radiolok/brainfuckpc/doc/core-memory.png

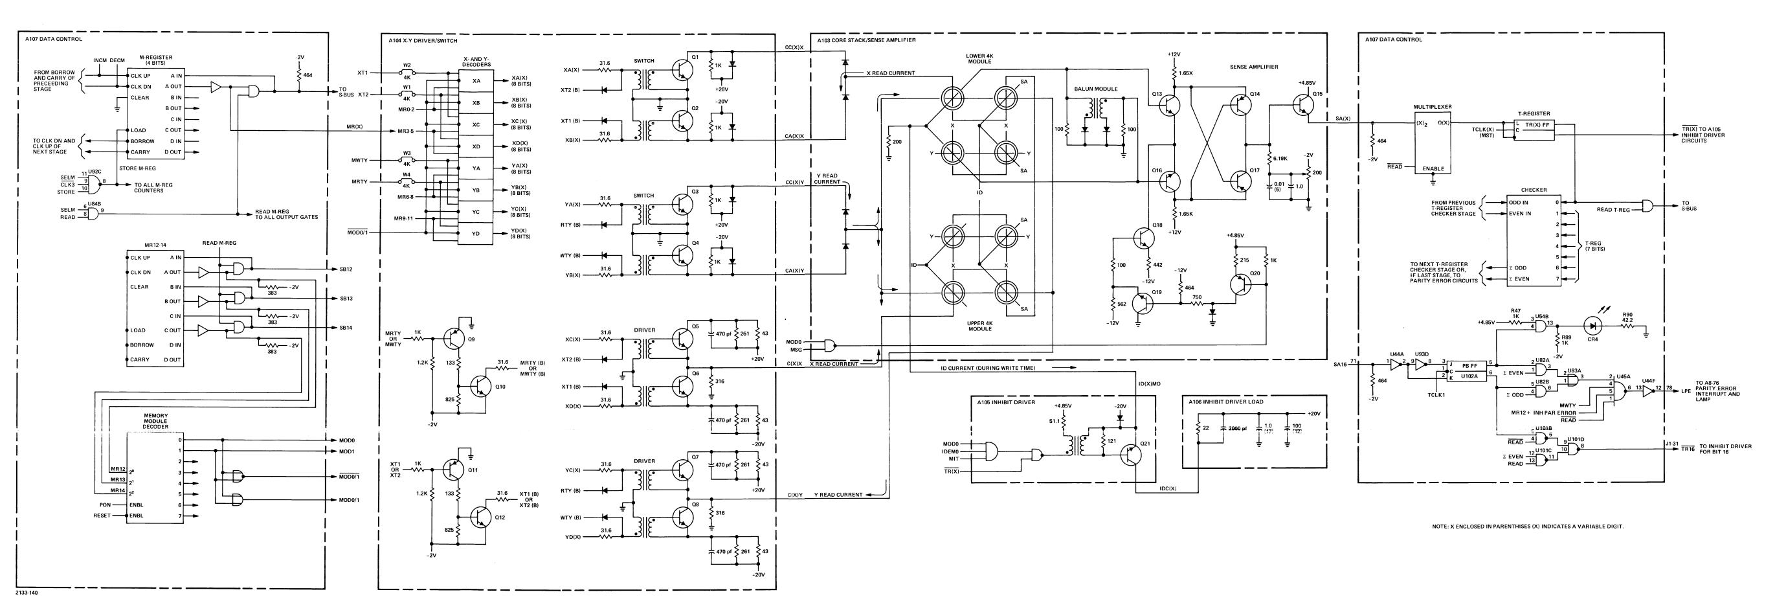
doc/core-memory.png
