radiolok/brainfuckpc/img/1bit_REG.png

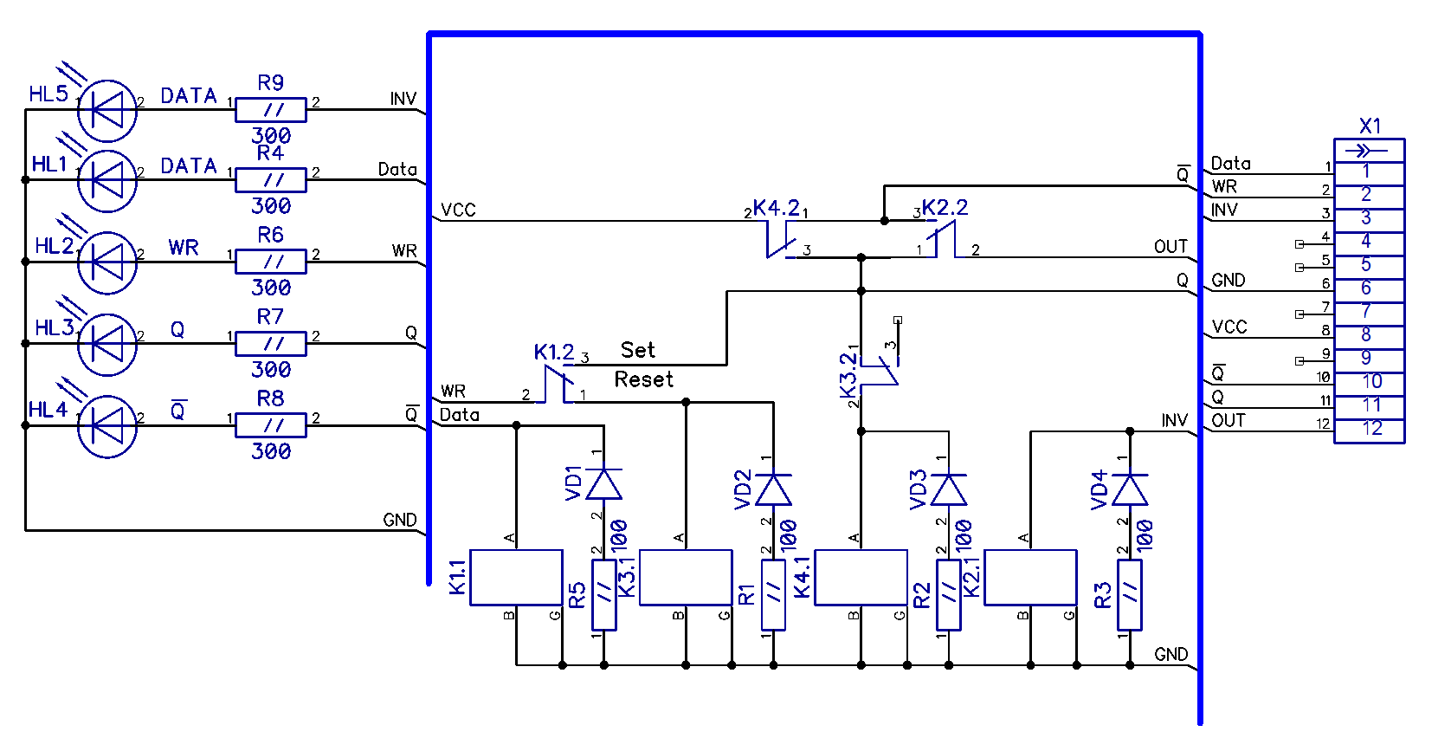
img/1bit_REG.png
