radiolok/brainfuckpc/img/16bit_parallel_SUM.png

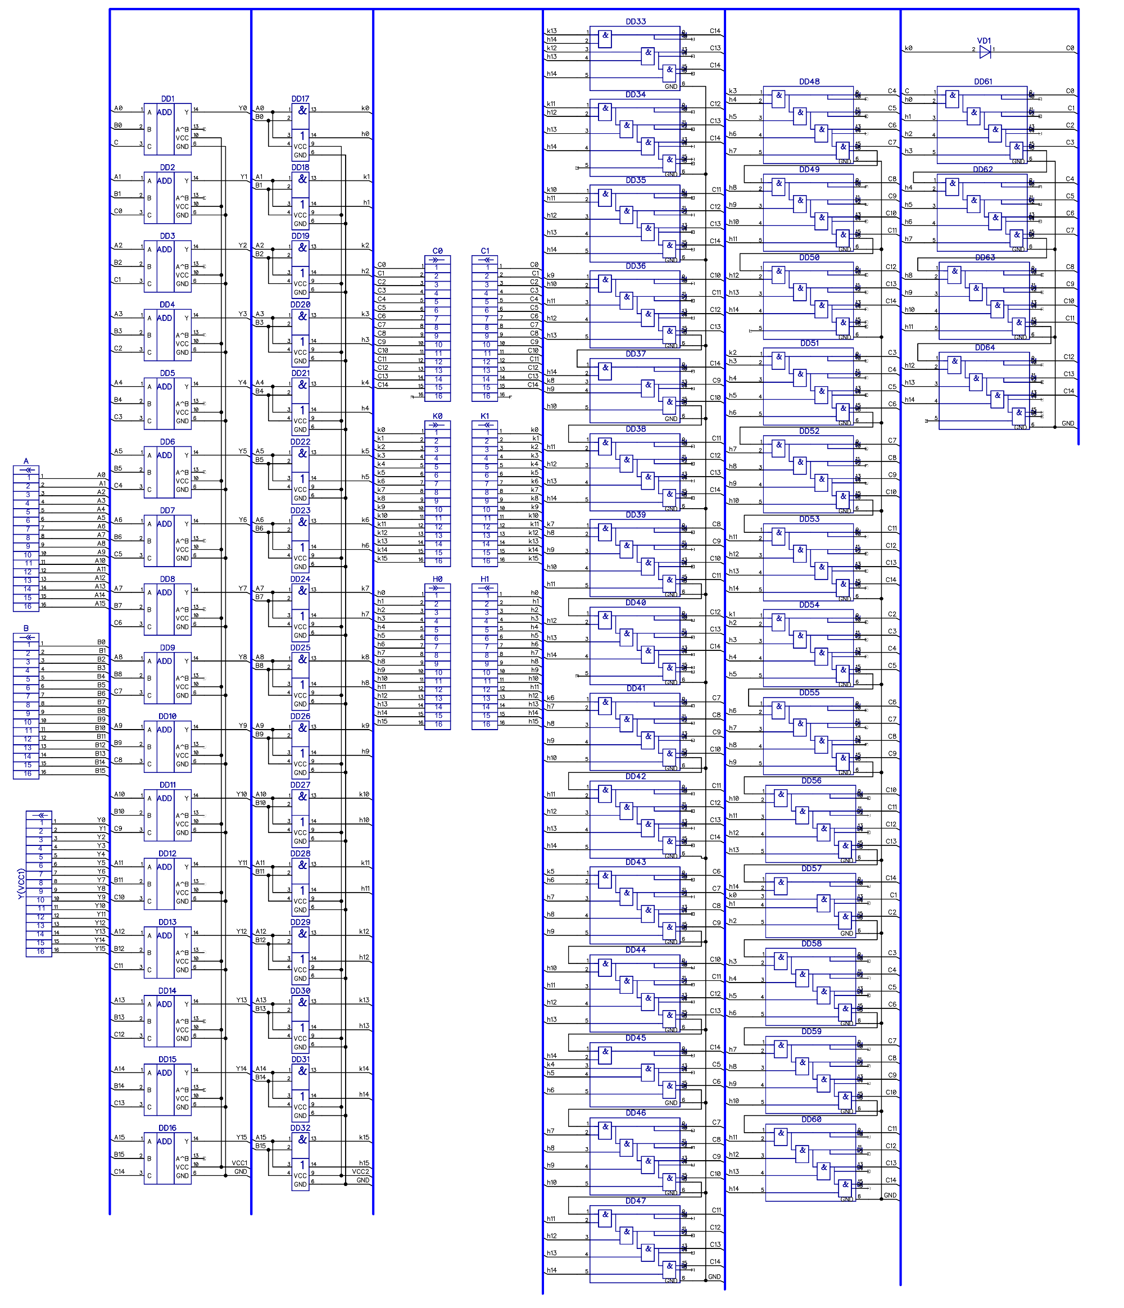
img/16bit_parallel_SUM.png
