radiolok/brainfuckpc/img/ALU.jpg

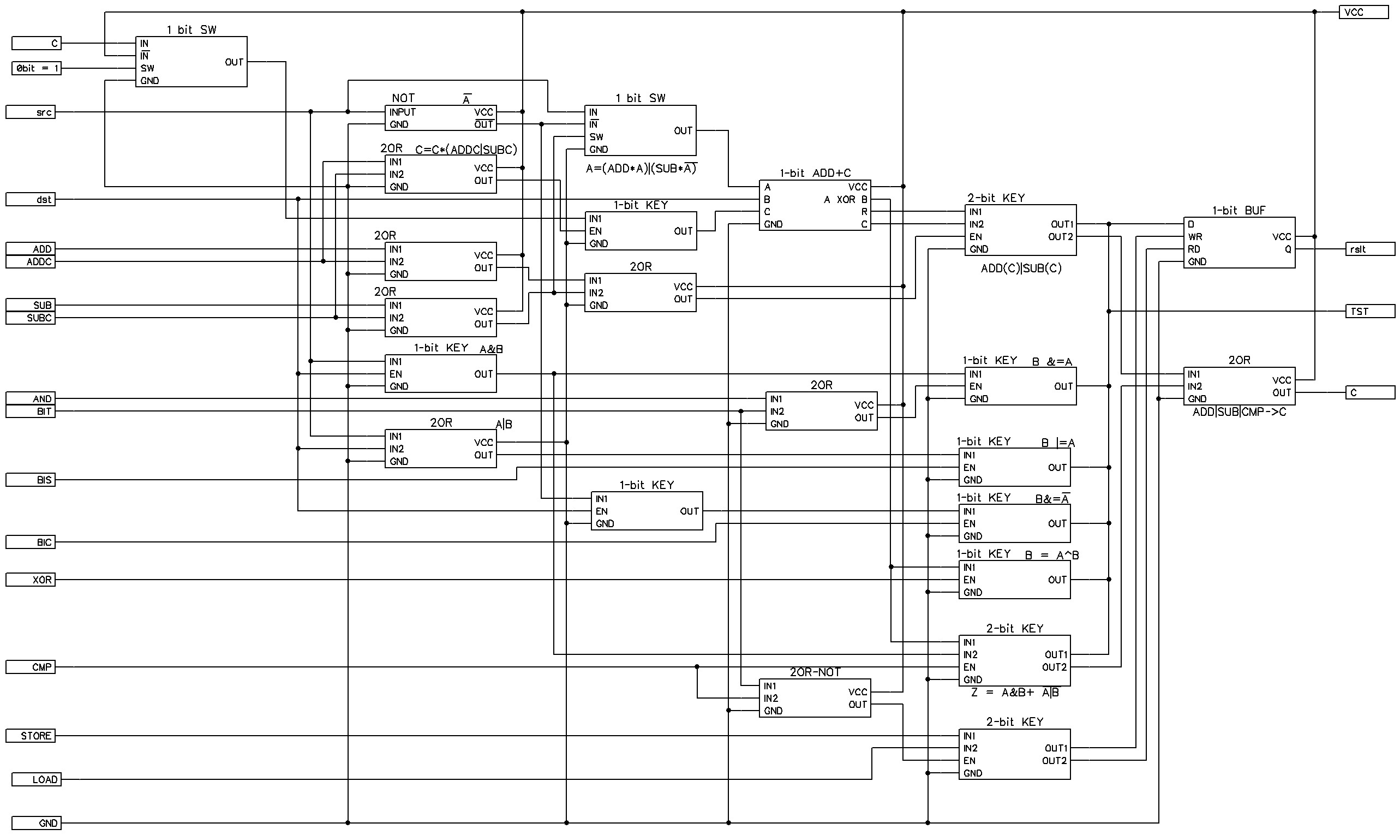
img/ALU.jpg
