radiolok/brainfuckpc/img/base_block_view.jpg

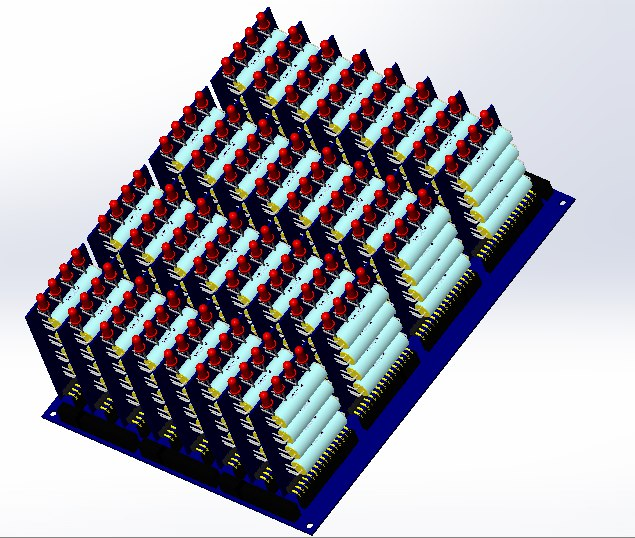
img/base_block_view.jpg
