radiolok/brainfuckpc/img/Brainfuck_PC_main_logic.png

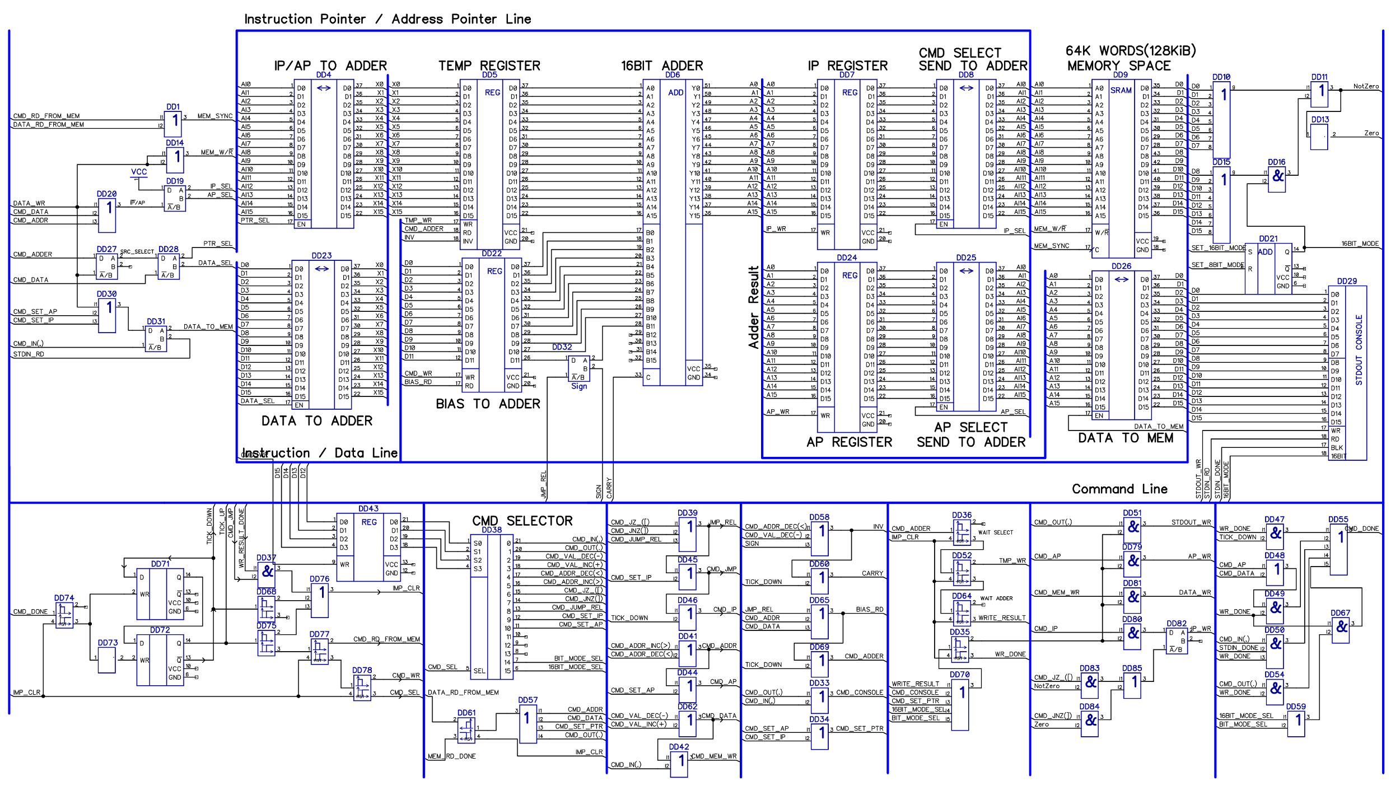
img/Brainfuck_PC_main_logic.png
