radiolok/brainfuckpc/img/ds.jpg

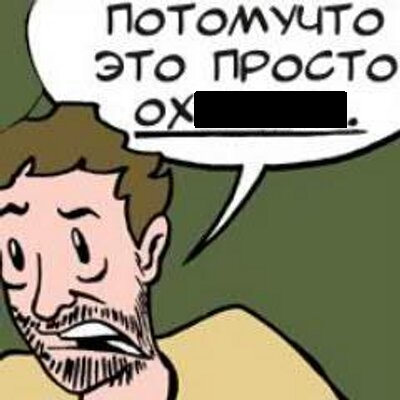
img/ds.jpg
