radiolok/brainfuckpc/img/logic.jpg

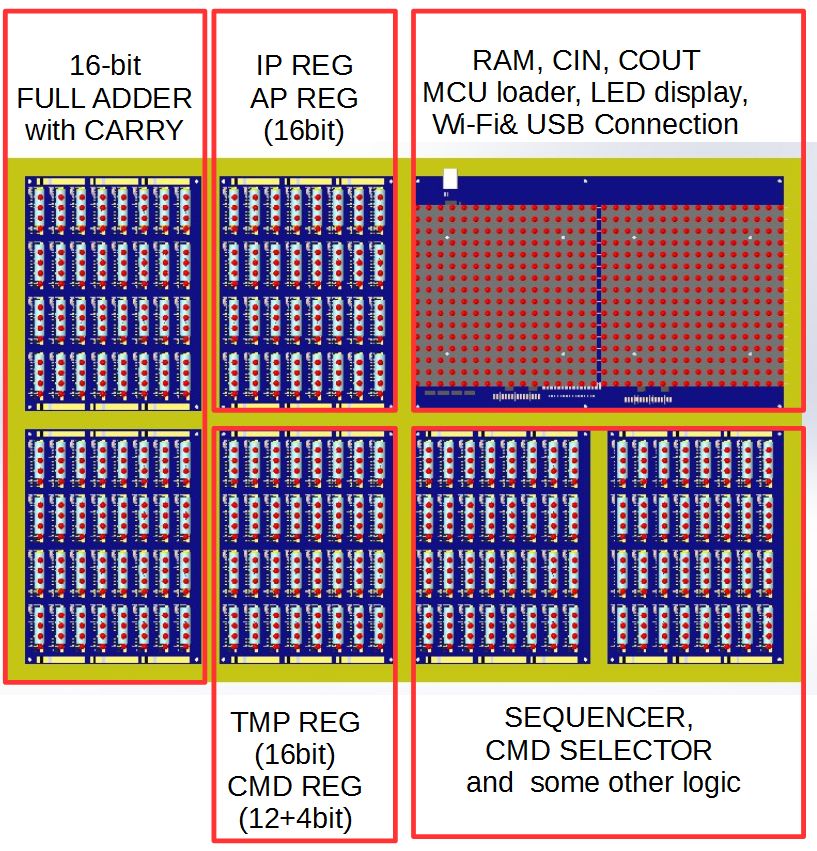
img/logic.jpg
