radiolok/brainfuckpc/img/logic_1.jpg

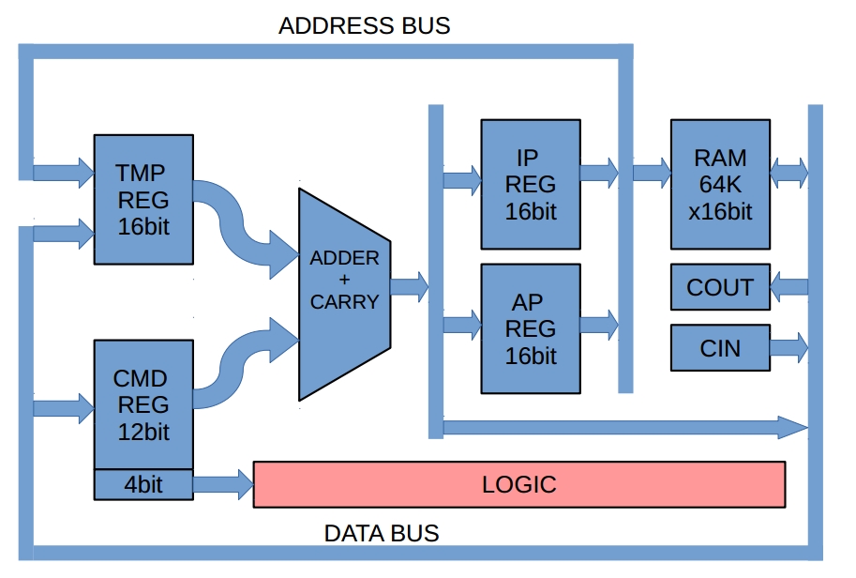
img/logic_1.jpg
