radiolok/brainfuckpc/img/memory_brd_real_2.jpg

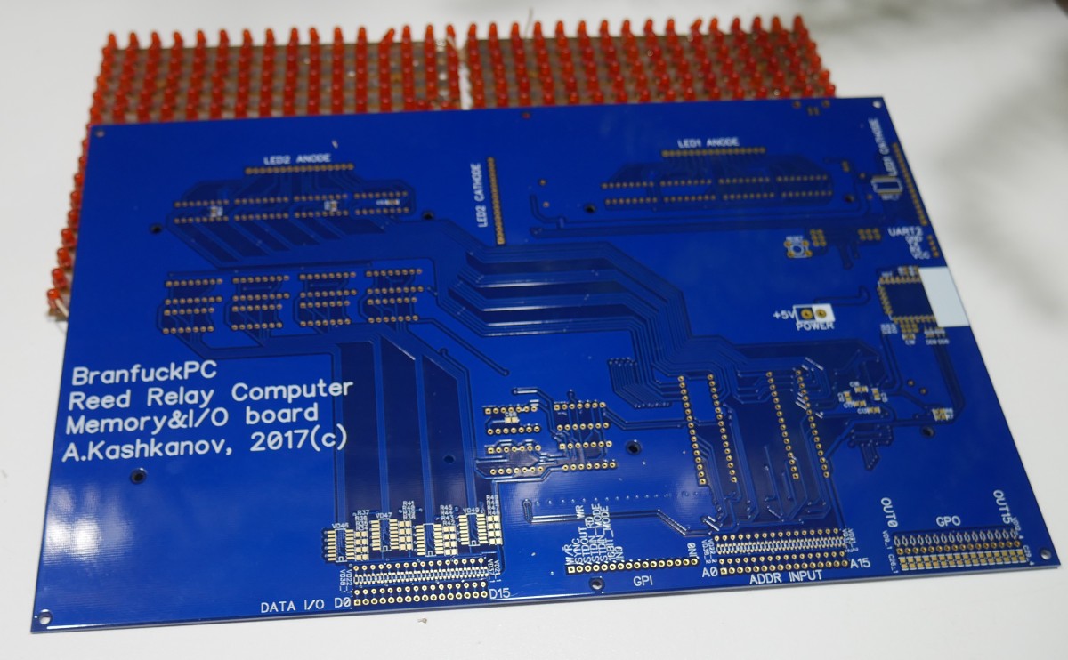
img/memory_brd_real_2.jpg
