radiolok/brainfuckpc/img/memorybrd_3d_bottom.jpg

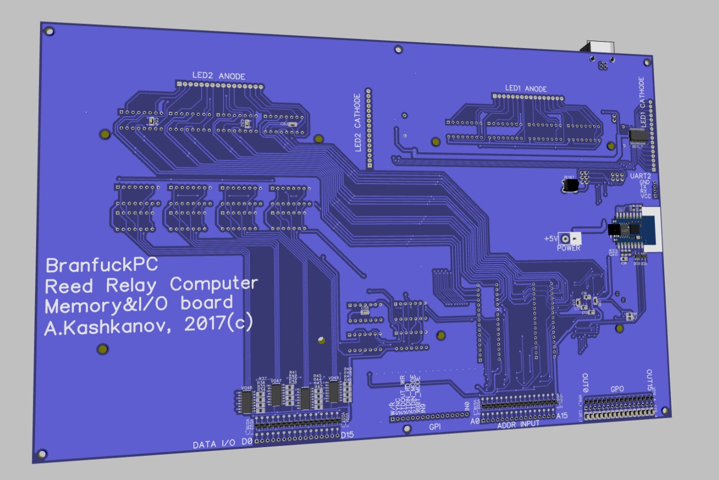
img/memorybrd_3d_bottom.jpg
