radiolok/brainfuckpc/img/module.jpg

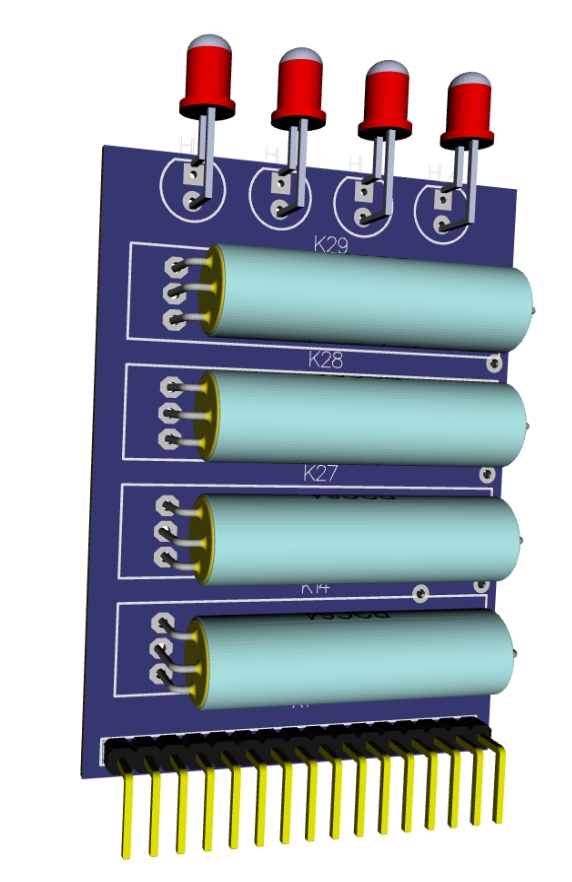
img/module.jpg
