radiolok/brainfuckpc/img/relays.jpg

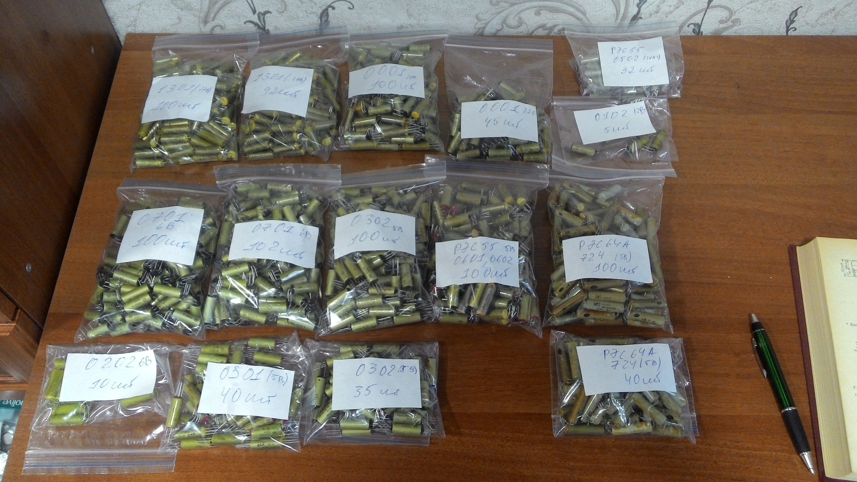
img/relays.jpg
