radiolok/brainfuckpc/img/reley_board.jpg

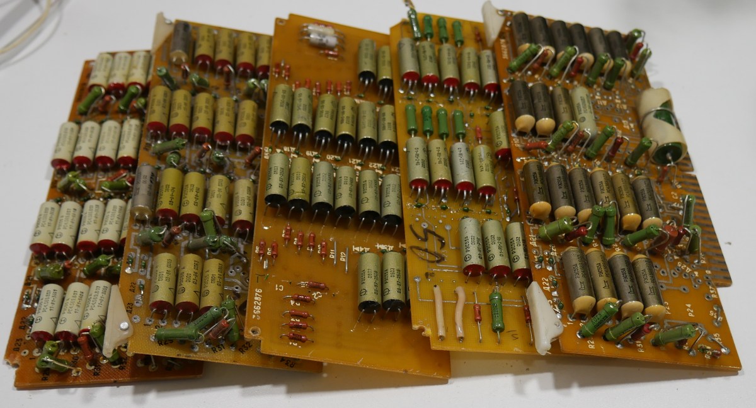
img/reley_board.jpg
