radiolok/brainfuckpc/img/sch1.jpg

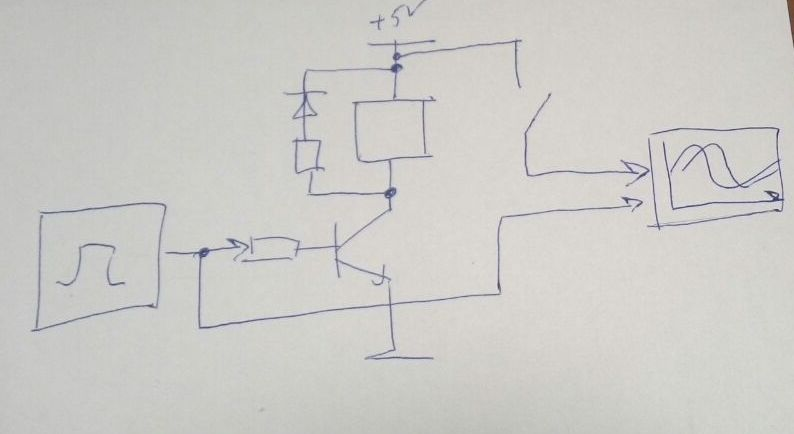
img/sch1.jpg
