radiolok/brainfuckpc/sch/Diode_module/3d_bottom.jpg

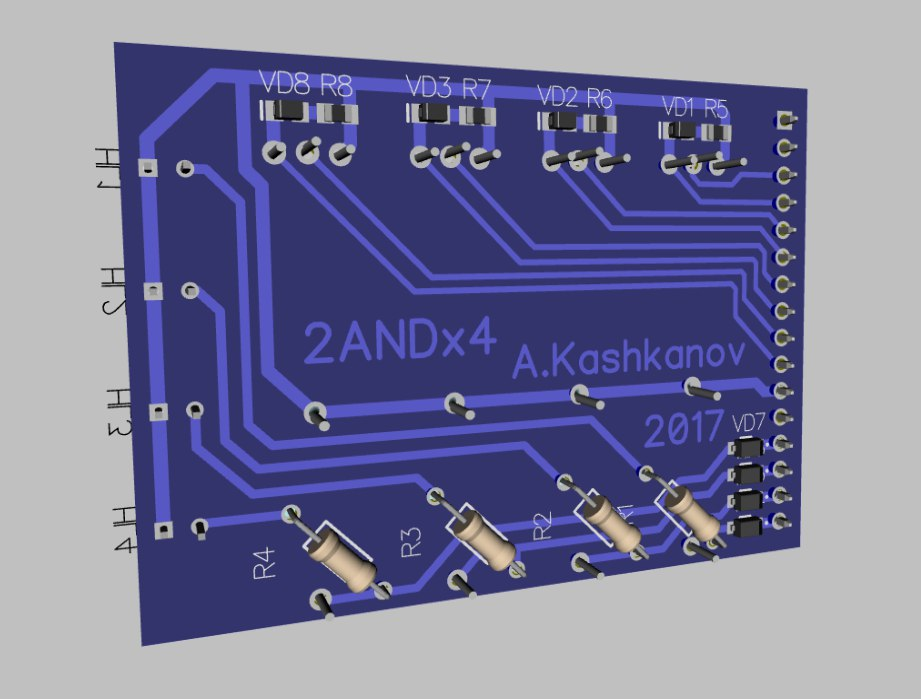
sch/Diode_module/3d_bottom.jpg
