radiolok/brainfuckpc/sch/Diode_module/diode_module.png

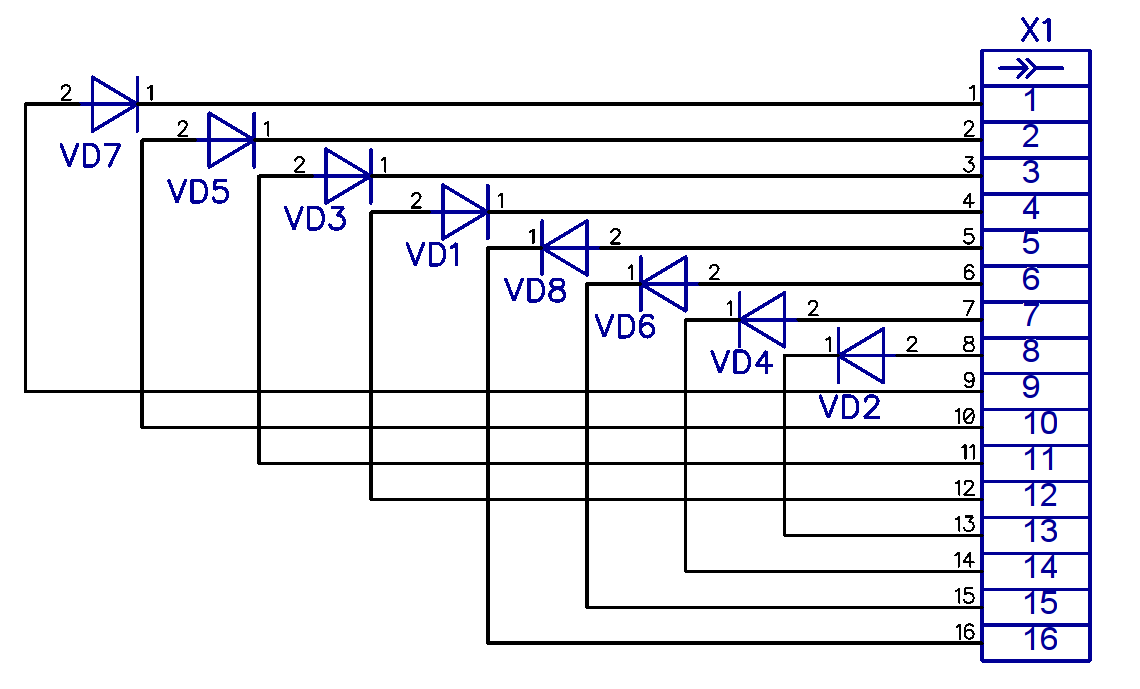
sch/Diode_module/diode_module.png
