radiolok/brainfuckpc/sch/MemoryBrd/pcb_bottom_3d.jpg

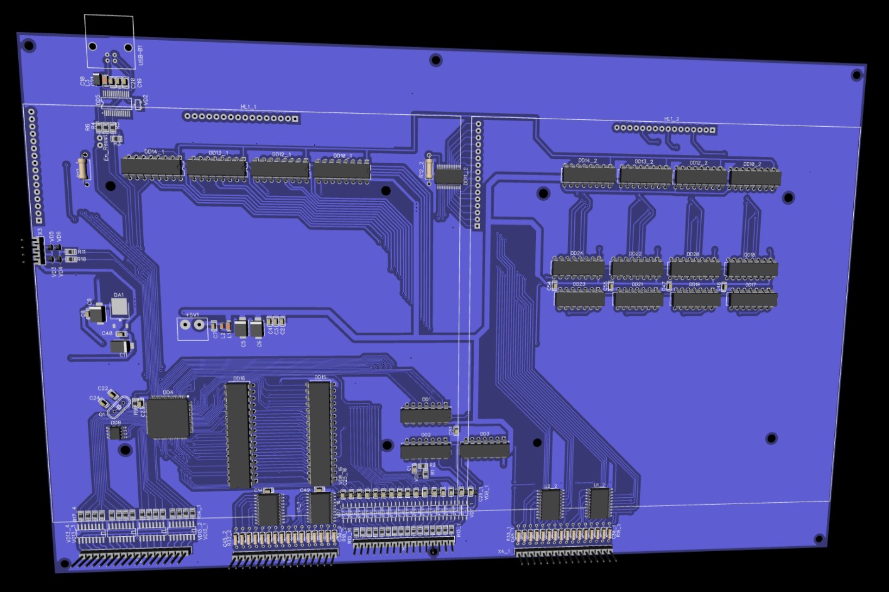
sch/MemoryBrd/pcb_bottom_3d.jpg
