radiolok/brainfuckpc/sch/MemoryBrd/pcb_top_3d.jpg

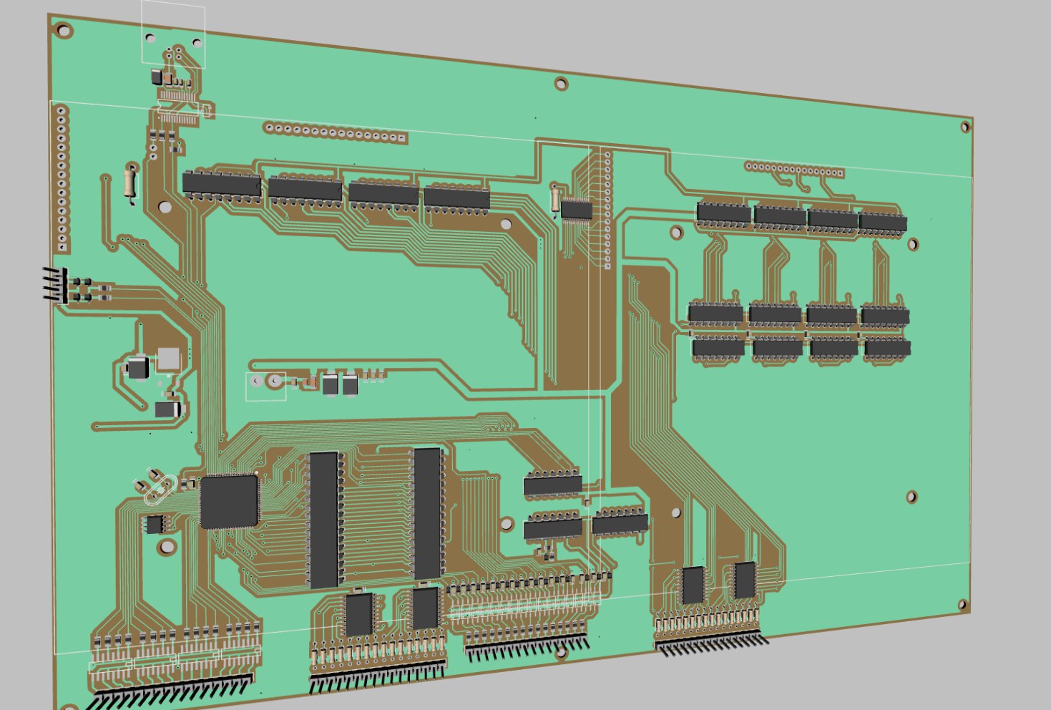
sch/MemoryBrd/pcb_top_3d.jpg
