radiolok/brainfuckpc/waveforms/ada-ads.png

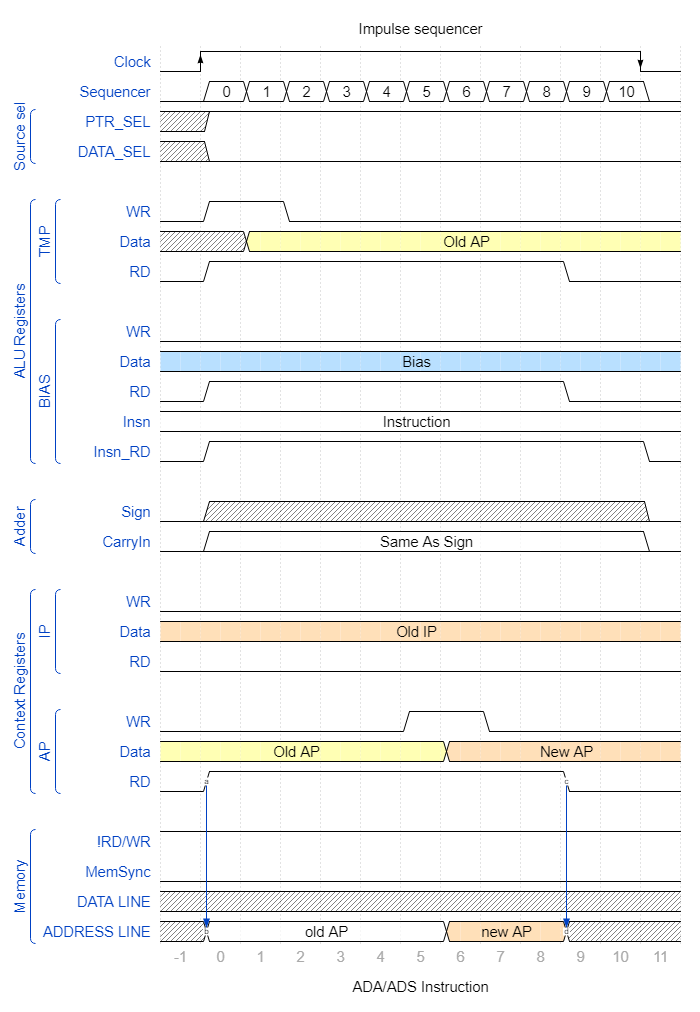
waveforms/ada-ads.png
