radiolok/brainfuckpc/waveforms/add-sub.png

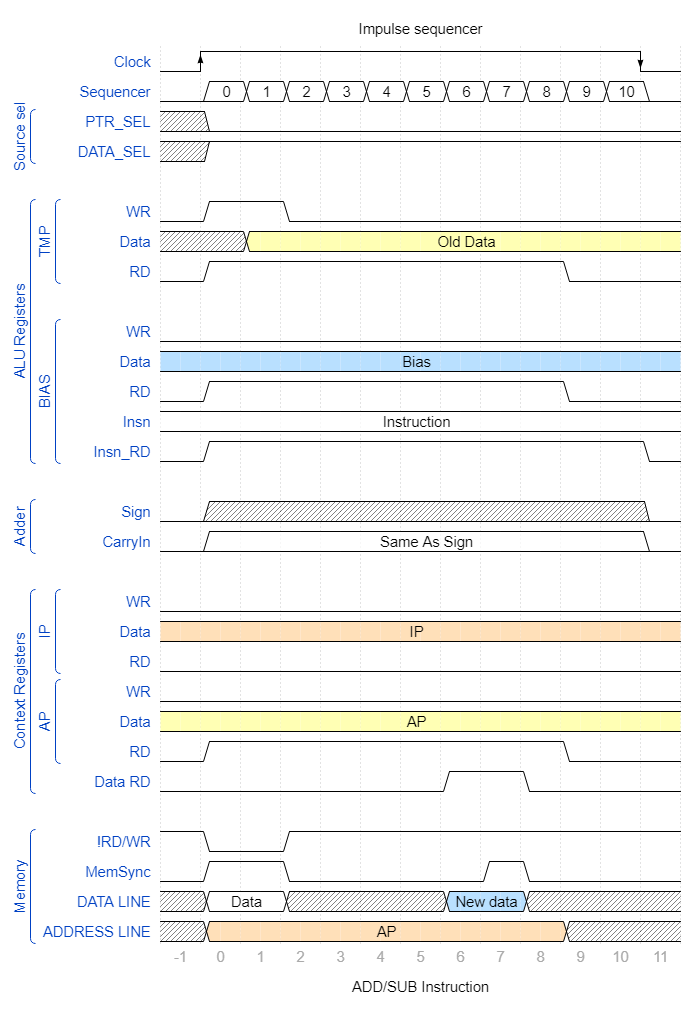
waveforms/add-sub.png
