radiolok/brainfuckpc/waveforms/cout.png

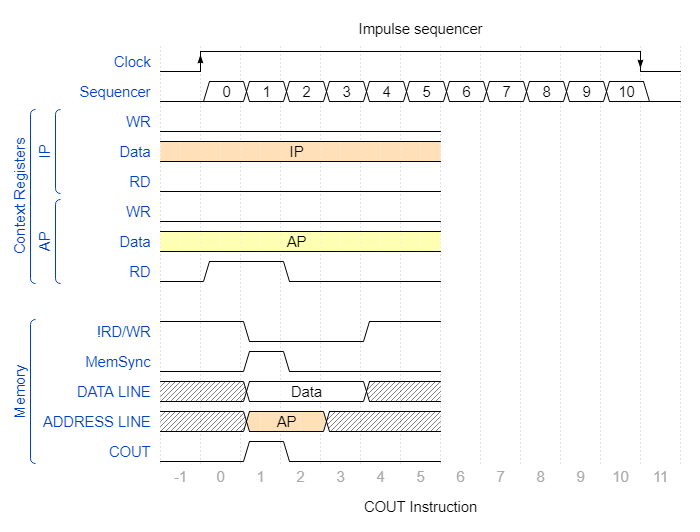
waveforms/cout.png
