radiolok/brainfuckpc/waveforms/insn_fetch.png

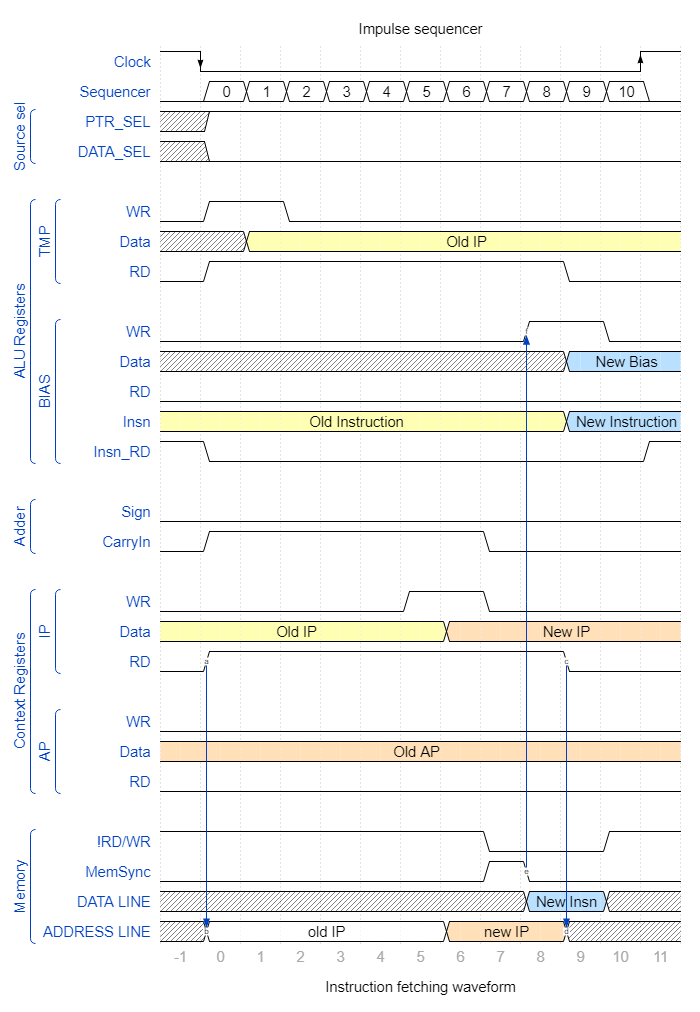
waveforms/insn_fetch.png
