radiolok/brainfuckpc/waveforms/jz_jnz_not_taken.png

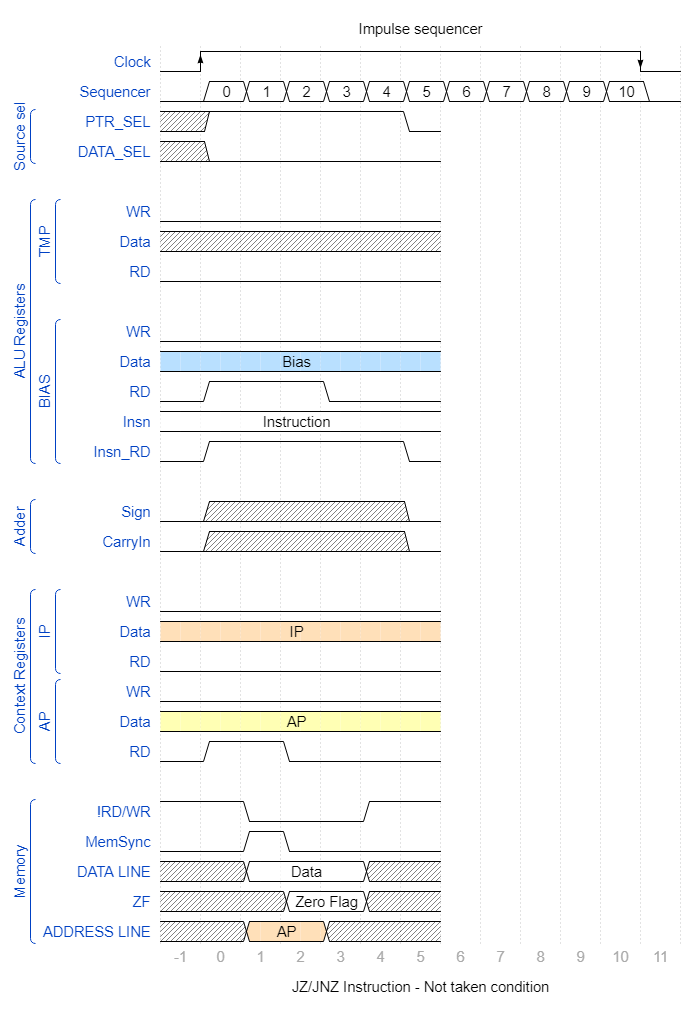
waveforms/jz_jnz_not_taken.png
