radiolok/brainfuckpc/waveforms/jz_jnz_taken.png

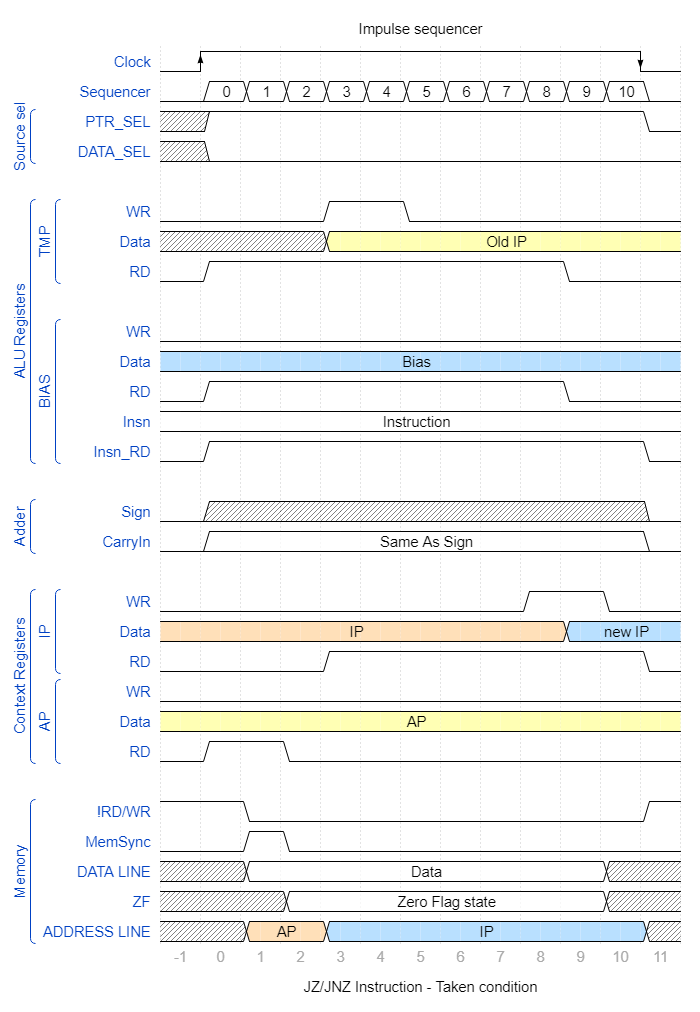
waveforms/jz_jnz_taken.png
