radiolok/brainfuckpc/fw/[DEPRECATE]/memorybrd_freertos/main.c

/*
 * FreeRTOS Kernel V10.1.1
 * Copyright (C) 2018 Amazon.com, Inc. or its affiliates.  All Rights Reserved.
 *
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
 * http://www.FreeRTOS.org
 * http://aws.amazon.com/freertos
 *
 * 1 tab == 4 spaces!
 */

/*
 * Creates all the demo application tasks, then starts the scheduler.  The WEB
 * documentation provides more details of the demo application tasks.
 *
 * Main. c also creates a task called "Check".  This only executes every three
 * seconds but has the highest priority so is guaranteed to get processor time.
 * Its main function is to check that all the other tasks are still operational.
 * Each task that does not flash an LED maintains a unique count that is
 * incremented each time the task successfully completes its function.  Should
 * any error occur within such a task the count is permanently halted.  The
 * check task inspects the count of each task to ensure it has changed since
 * the last time the check task executed.  If all the count variables have
 * changed all the tasks are still executing error free, and the check task
 * toggles an LED.  Should any task contain an error at any time the LED toggle
 * will stop.
 *
 * The LED flash and communications test tasks do not maintain a count.
 */

/*
Changes from V1.2.0

	+ Changed the baud rate for the serial test from 19200 to 57600.

Changes from V1.2.3

	+ The integer and comtest tasks are now used when the cooperative scheduler
	  is being used.  Previously they were only used with the preemptive
	  scheduler.

Changes from V1.2.5

	+ Set the baud rate to 38400.  This has a smaller error percentage with an
	  8MHz clock (according to the manual).

Changes from V2.0.0

	+ Delay periods are now specified using variables and constants of
	  TickType_t rather than unsigned long.

Changes from V2.6.1

	+ The IAR and WinAVR AVR ports are now maintained separately.

Changes from V4.0.5

	+ Modified to demonstrate the use of co-routines.

*/

#include <stdlib.h>
#include <string.h>

#ifdef GCC_MEGA_AVR
	/* EEPROM routines used only with the WinAVR compiler. */
	#include <avr/eeprom.h>
#endif

/* Scheduler include files. */
#include "FreeRTOS.h"
#include "task.h"
#include "croutine.h"

/* Demo file headers. */
#include "PollQ.h"
#include "integer.h"
#include "serial.h"
#include "comtest.h"
#include "crflash.h"
#include "print.h"


/* Priority definitions for most of the tasks in the demo application.  Some
tasks just use the idle priority. */
#define mainLED_TASK_PRIORITY			( tskIDLE_PRIORITY + 1 )
#define mainCOM_TEST_PRIORITY			( tskIDLE_PRIORITY + 2 )
#define mainQUEUE_POLL_PRIORITY			( tskIDLE_PRIORITY + 2 )
#define mainCHECK_TASK_PRIORITY			( tskIDLE_PRIORITY + 3 )

/* Baud rate used by the serial port tasks. */
#define mainCOM_TEST_BAUD_RATE			( ( unsigned long ) 38400 )

/* LED used by the serial port tasks.  This is toggled on each character Tx,
and mainCOM_TEST_LED + 1 is toggles on each character Rx. */
#define mainCOM_TEST_LED				( 4 )

/* LED that is toggled by the check task.  The check task periodically checks
that all the other tasks are operating without error.  If no errors are found
the LED is toggled.  If an error is found at any time the LED is never toggles
again. */
#define mainCHECK_TASK_LED				( 7 )

/* The period between executions of the check task. */
#define mainCHECK_PERIOD				( ( TickType_t ) 3000 / portTICK_PERIOD_MS  )

/* An address in the EEPROM used to count resets.  This is used to check that
the demo application is not unexpectedly resetting. */
#define mainRESET_COUNT_ADDRESS			( ( void * ) 0x50 )


static void prvCheckOtherTasksAreStillRunning( void );

/*-----------------------------------------------------------*/

int main( void )
{

	/* In this port, to use preemptive scheduler define configUSE_PREEMPTION
	as 1 in portmacro.h.  To use the cooperative scheduler define
	configUSE_PREEMPTION as 0. */
	vTaskStartScheduler();

	return 0;
}
/*-----------------------------------------------------------*/

static void vErrorChecks( void *pvParameters )
{
static volatile unsigned long ulDummyVariable = 3UL;

	/* The parameters are not used. */
	( void ) pvParameters;

	/* Cycle for ever, delaying then checking all the other tasks are still
	operating without error. */
	for( ;; )
	{
		vTaskDelay( mainCHECK_PERIOD );

		/* Perform a bit of 32bit maths to ensure the registers used by the
		integer tasks get some exercise. The result here is not important -
		see the demo application documentation for more info. */
		ulDummyVariable *= 3;

		prvCheckOtherTasksAreStillRunning();
	}
}
/*-----------------------------------------------------------*/

static void prvCheckOtherTasksAreStillRunning( void )
{
static portBASE_TYPE xErrorHasOccurred = pdFALSE;


}
/*-----------------------------------------------------------*/

static void prvIncrementResetCount( void )
{
unsigned char ucCount;

	eeprom_read_block( &ucCount, mainRESET_COUNT_ADDRESS, sizeof( ucCount ) );
	ucCount++;
	eeprom_write_byte( mainRESET_COUNT_ADDRESS, ucCount );
}
/*-----------------------------------------------------------*/
