radiolok/brainfuckpc/fw/mcuUtil/uart.h

#ifndef UART_H
#define UART_H
/************************************************************************
Title:    Interrupt UART library with receive/transmit circular buffers
Author:   Peter Fleury <pfleury@gmx.ch>   http://jump.to/fleury
Support:   Artem Kashkanov<pcb@rlntech.org> http://hg.rlntech.org/uart
File:     $Id: uart.h,v 1.8.2.1 2007/07/01 11:14:38 peter Exp $
Software: AVR-GCC 4.1, AVR Libc 1.4
Hardware: any AVR with built-in UART, tested on AT90S8515 & ATmega8 at 4 Mhz
License:  GNU General Public License 
Usage:    see Doxygen manual

LICENSE:
    Copyright (C) 2006 Peter Fleury

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
************************************************************************/

/************************************************************************
uart_available, uart_flush, uart1_available, and uart1_flush functions
were adapted from the Arduino HardwareSerial.h library by Tim Sharpe on 
11 Jan 2009.  The license info for HardwareSerial.h is as follows:

  HardwareSerial.h - Hardware serial library for Wiring
  Copyright (c) 2006 Nicholas Zambetti.  All right reserved.

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
  You should have received a copy of the GNU Lesser General Public
  License along with this library; if not, write to the Free Software
  Foundation, Inc., 51 Franklin St, Fifth Floor, Boston, MA  02110-1301  USA
************************************************************************/

/************************************************************************
Changelog for modifications made by Tim Sharpe, starting with the current
  library version on his Web site as of 05/01/2009. 

Date        Description
=========================================================================
05/12/2009  Added Arduino-style available() and flush() functions for both
			supported UARTs.  Really wanted to keep them out of the library, so
			that it would be as close as possible to Peter Fleury's original
			library, but has scoping issues accessing internal variables from
			another program.  Go C!

************************************************************************/

/** 
 *  This library can be used to transmit and receive data through the built in UART. 
 *
 *  An interrupt is generated when the UART has finished transmitting or
 *  receiving a byte. The interrupt handling routines use circular buffers
 *  for buffering received and transmitted data.
 *
 *  The UART_RX_BUFFER_SIZE and UART_TX_BUFFER_SIZE constants define
 *  the size of the circular buffers in bytes. Note that these constants must be a power of 2.
 *  You may need to adapt this constants to your target and your application by adding 
 *  CDEFS += -DUART_RX_BUFFER_SIZE=nn -DUART_RX_BUFFER_SIZE=nn to your Makefile.
 *
 *  @note Based on Atmel Application Note AVR306
 *  @author Peter Fleury pfleury@gmx.ch  http://jump.to/fleury
 */
 


#if (__GNUC__ * 100 + __GNUC_MINOR__) < 304
#error "This library requires AVR-GCC 3.4 or later, update to newer AVR-GCC compiler !"
#endif

#include <stdint.h>

#define UART_BAUD_SELECT(baudRate,xtalCpu) ((xtalCpu)/((baudRate)*16l)-1)


#define UART_BAUD_SELECT_DOUBLE_SPEED(baudRate,xtalCpu) (((xtalCpu)/((baudRate)*8l)-1)|0x8000)


/** Size of the circular receive buffer, must be power of 2 */
#ifndef UART_RX_BUFFER_SIZE
#define UART_RX_BUFFER_SIZE 16
#endif
/** Size of the circular transmit buffer, must be power of 2 */
#ifndef UART_TX_BUFFER_SIZE
#define UART_TX_BUFFER_SIZE 32
#endif



#define UART_FRAME_ERROR      0x00              /* Framing Error by UART       */
#define UART_OVERRUN_ERROR    0x00              /* Overrun condition by UART   */
#define UART_BUFFER_OVERFLOW  0x00              /* receive ringbuffer overflow */
#define UART_NO_DATA          0x00              /* no receive data available   */


#define UART_PARITY_NONE 0x00
#define UART_PARITY_ODD 0x01
#define UART_PARITY_EVEN 0x02


 void uart_init(unsigned int baudrate);
 void uart_putc(unsigned char data);
uint8_t uart_getc(void);  
 void uart_puts(const char *s );  
void uart_puts_p(const char *s );  
 #define uart_puts_P(__s)       uart_puts_p(PSTR(__s)) 
 uint8_t uart_available(void); 
void uart_flush(void); 
void uart_print(int16_t val, int8_t base);

void uart_set_parity(uint8_t);
 
  #if  defined(__AVR_ATmega2560__) || defined(__AVR_ATmega1280__)
	 void uart2_init(unsigned int baudrate);
	 uint8_t uart2_getc(void);
	 void uart2_putc(unsigned char data);
	 void uart2_puts(const char *s );
	 void uart2_puts_p(const char *s );
	 #define uart2_puts_P(__s)       uart2_puts_p(PSTR(__s))
	 int uart2_available(void);
	 void uart2_flush(void);

	 void uart3_init(unsigned int baudrate);
	 uint8_t uart3_getc(void);
	 void uart3_putc(unsigned char data);
	 void uart3_puts(const char *s );
	 void uart3_puts_p(const char *s );
	 #define uart3_puts_P(__s)       uart3_puts_p(PSTR(__s))
	 int uart3_available(void);
	 void uart3_flush(void);
	 
	 /** @brief  Initialize USART1 (only available on selected ATmegas) @see uart_init */
	 void uart1_init(unsigned int baudrate);
	 /** @brief  Get received byte of USART1 from ringbuffer. (only available on selected ATmega) @see uart_getc */
	 uint8_t uart1_getc(void);
	 /** @brief  Put byte to ringbuffer for transmitting via USART1 (only available on selected ATmega) @see uart_putc */
	 void uart1_putc(unsigned char data);
	 /** @brief  Put string to ringbuffer for transmitting via USART1 (only available on selected ATmega) @see uart_puts */
	 void uart1_puts(const char *s );
	 /** @brief  Put string from program memory to ringbuffer for transmitting via USART1 (only available on selected ATmega) @see uart_puts_p */
	 void uart1_puts_p(const char *s );
	 /** @brief  Macro to automatically put a string constant into program memory */
	 #define uart1_puts_P(__s)       uart1_puts_p(PSTR(__s))
	 /** @brief   Return number of bytes waiting in the receive buffer */
	 int uart1_available(void);
	 /** @brief   Flush bytes waiting in receive buffer */
	 void uart1_flush(void);

#endif









#endif // UART_H 
